Squirco/SensorNode-2-SensorHub/firmware/src/LED.h

#ifndef _LED_H_
#define _LED_H_

#include <stdint.h>
#include <avr/pgmspace.h>

extern const uint16_t cie[101] PROGMEM = {
	0, 1, 2, 3, 5, 6, 7, 8, 9, 10,
	12, 13, 14, 16, 18, 20, 21, 24, 26, 28,
	31, 33, 36, 39, 42, 45, 49, 52, 56, 60,
	64, 68, 72, 77, 82, 87, 92, 98, 103, 109,
	115, 121, 128, 135, 142, 149, 156, 164, 172, 180,
	188, 197, 206, 215, 225, 235, 245, 255, 266, 276,
	288, 299, 311, 323, 336, 348, 361, 375, 388, 402,
	417, 432, 447, 462, 478, 494, 510, 527, 544, 562,
	580, 598, 617, 636, 655, 675, 696, 716, 737, 759,
	781, 803, 826, 849, 872, 896, 921, 946, 971, 997,
	1023
};

#endif
